njeff/portaled/SPICE/PowerOR.asc

D1: schottky; MBRS140
R2: res; 6
R3: res; 100k
U1: DMG2305UX
V1: voltage; PULSE(0 5 0 0.0001 0.0001 0.5 1 4)
V2: voltage; PULSE(0 4 0 0 0.00001 4.5)
Named nets: 0
.tran 5
